UNAWatch/una-hardware/una-watch/electronics/UNAlink_BLUENRG2/UNAlink_BLUENRG2 Rev1.4 Assembly.pdf

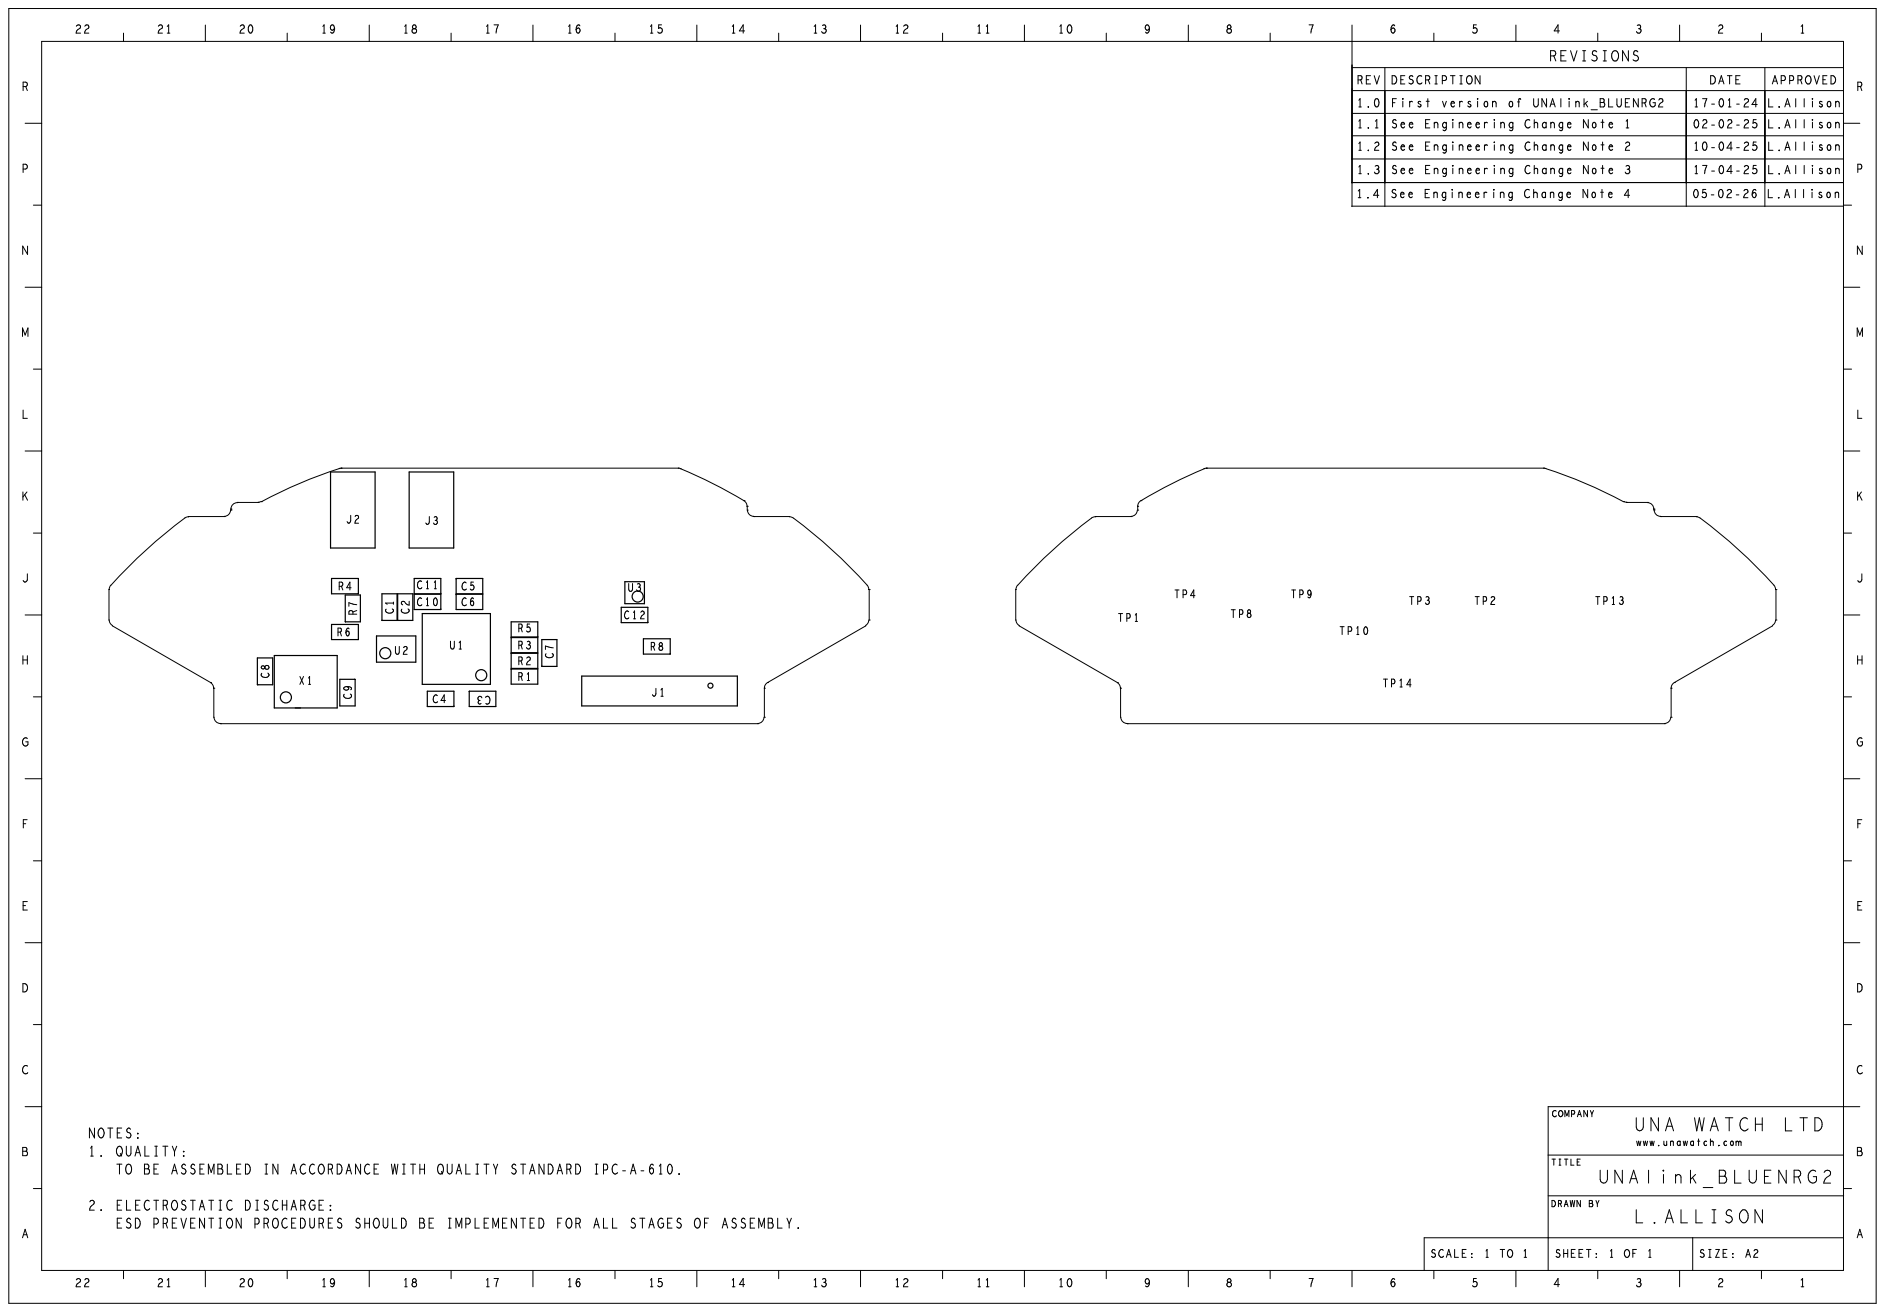
[picture p36: page 1]
