UNAWatch/una-hardware/una-watch/electronics/UNAlink_BLUENRG2/UNAlink_BLUENRG2 Rev1.4 Fabrication.pdf

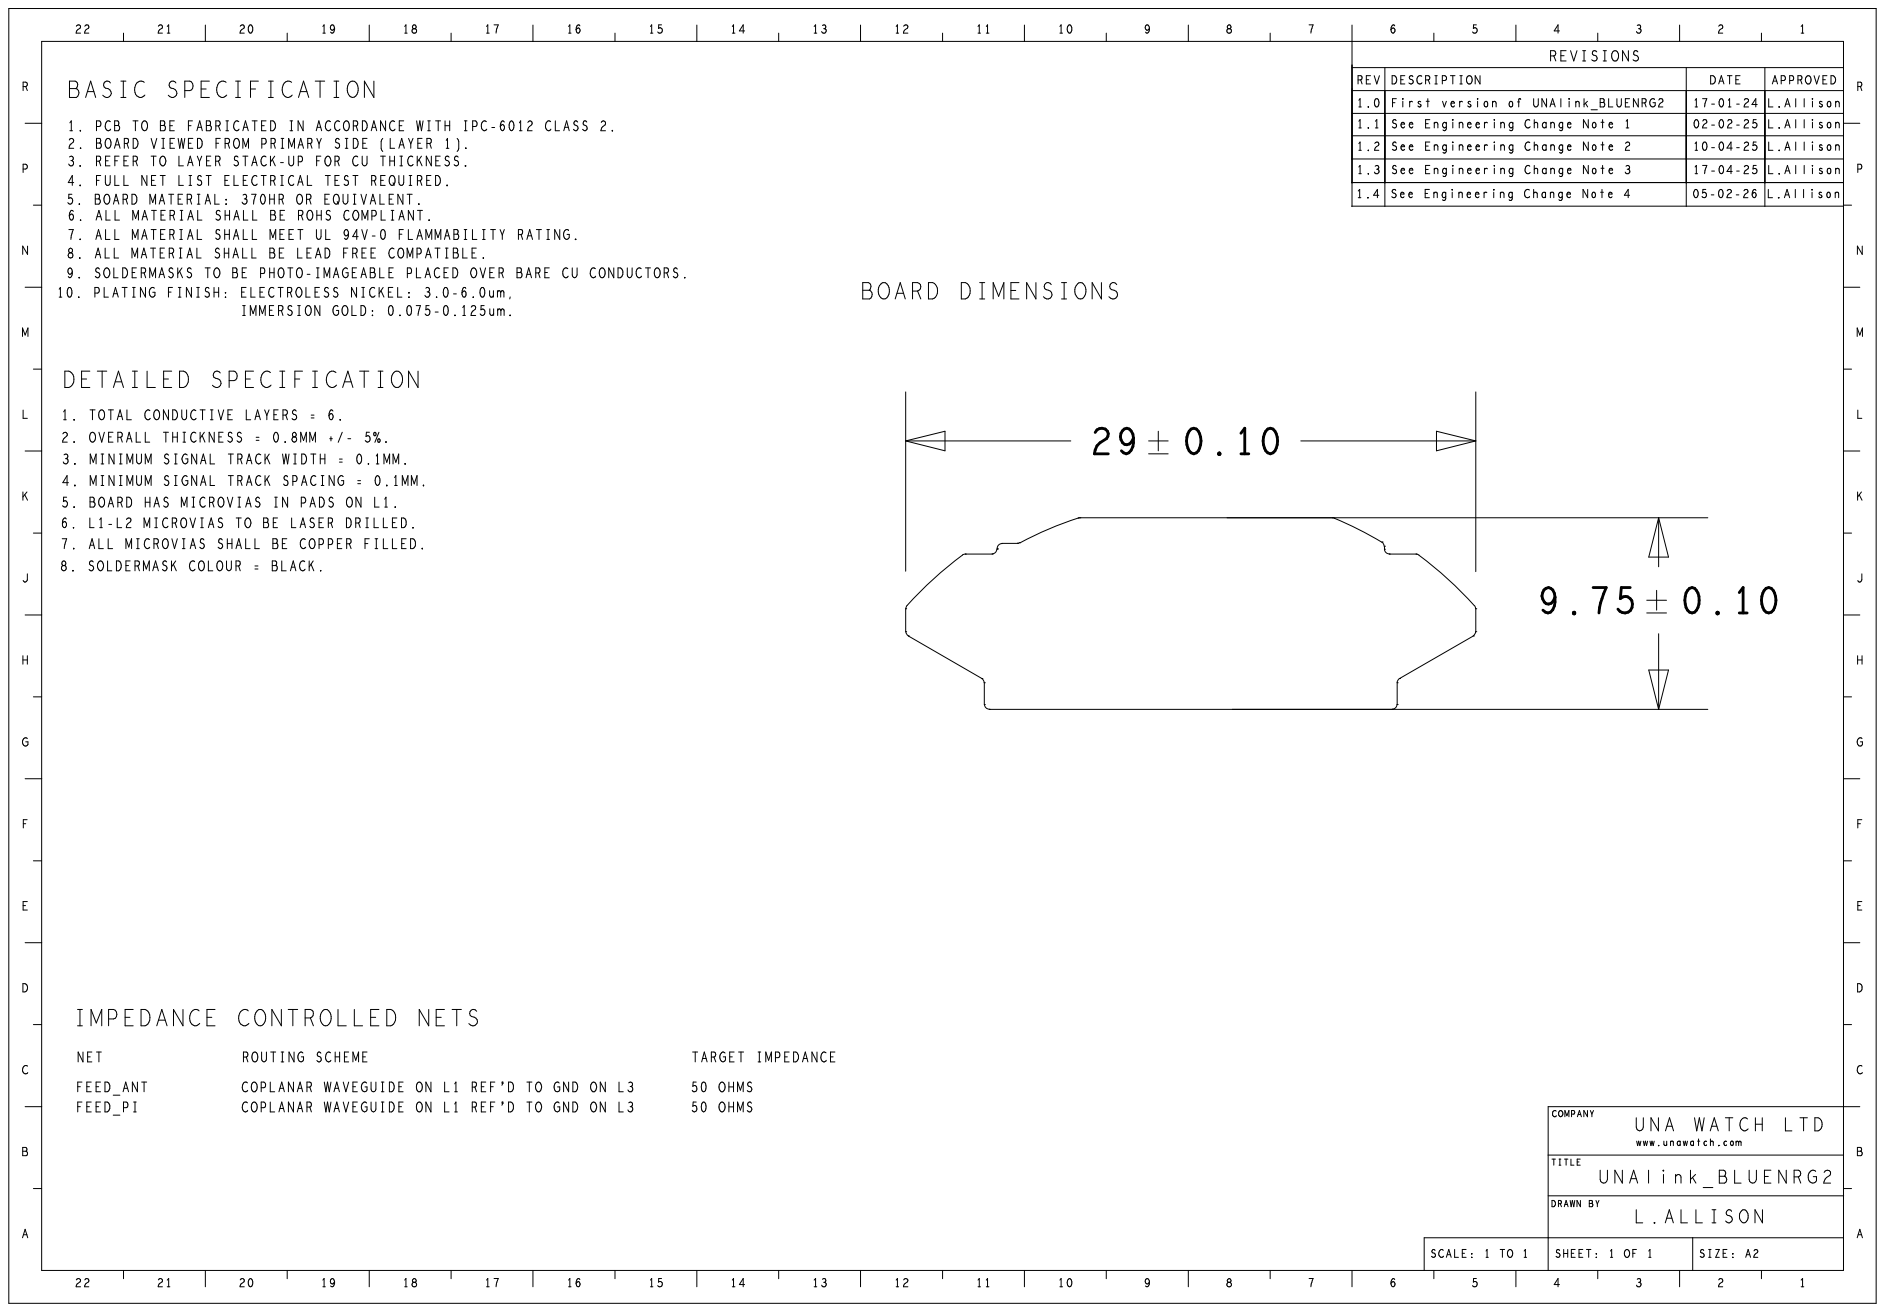
[picture p37: page 1]
