UNAWatch/una-hardware/una-watch/electronics/UNAview_LS012/UNAview_LS012 Rev1.3 Assembly.pdf

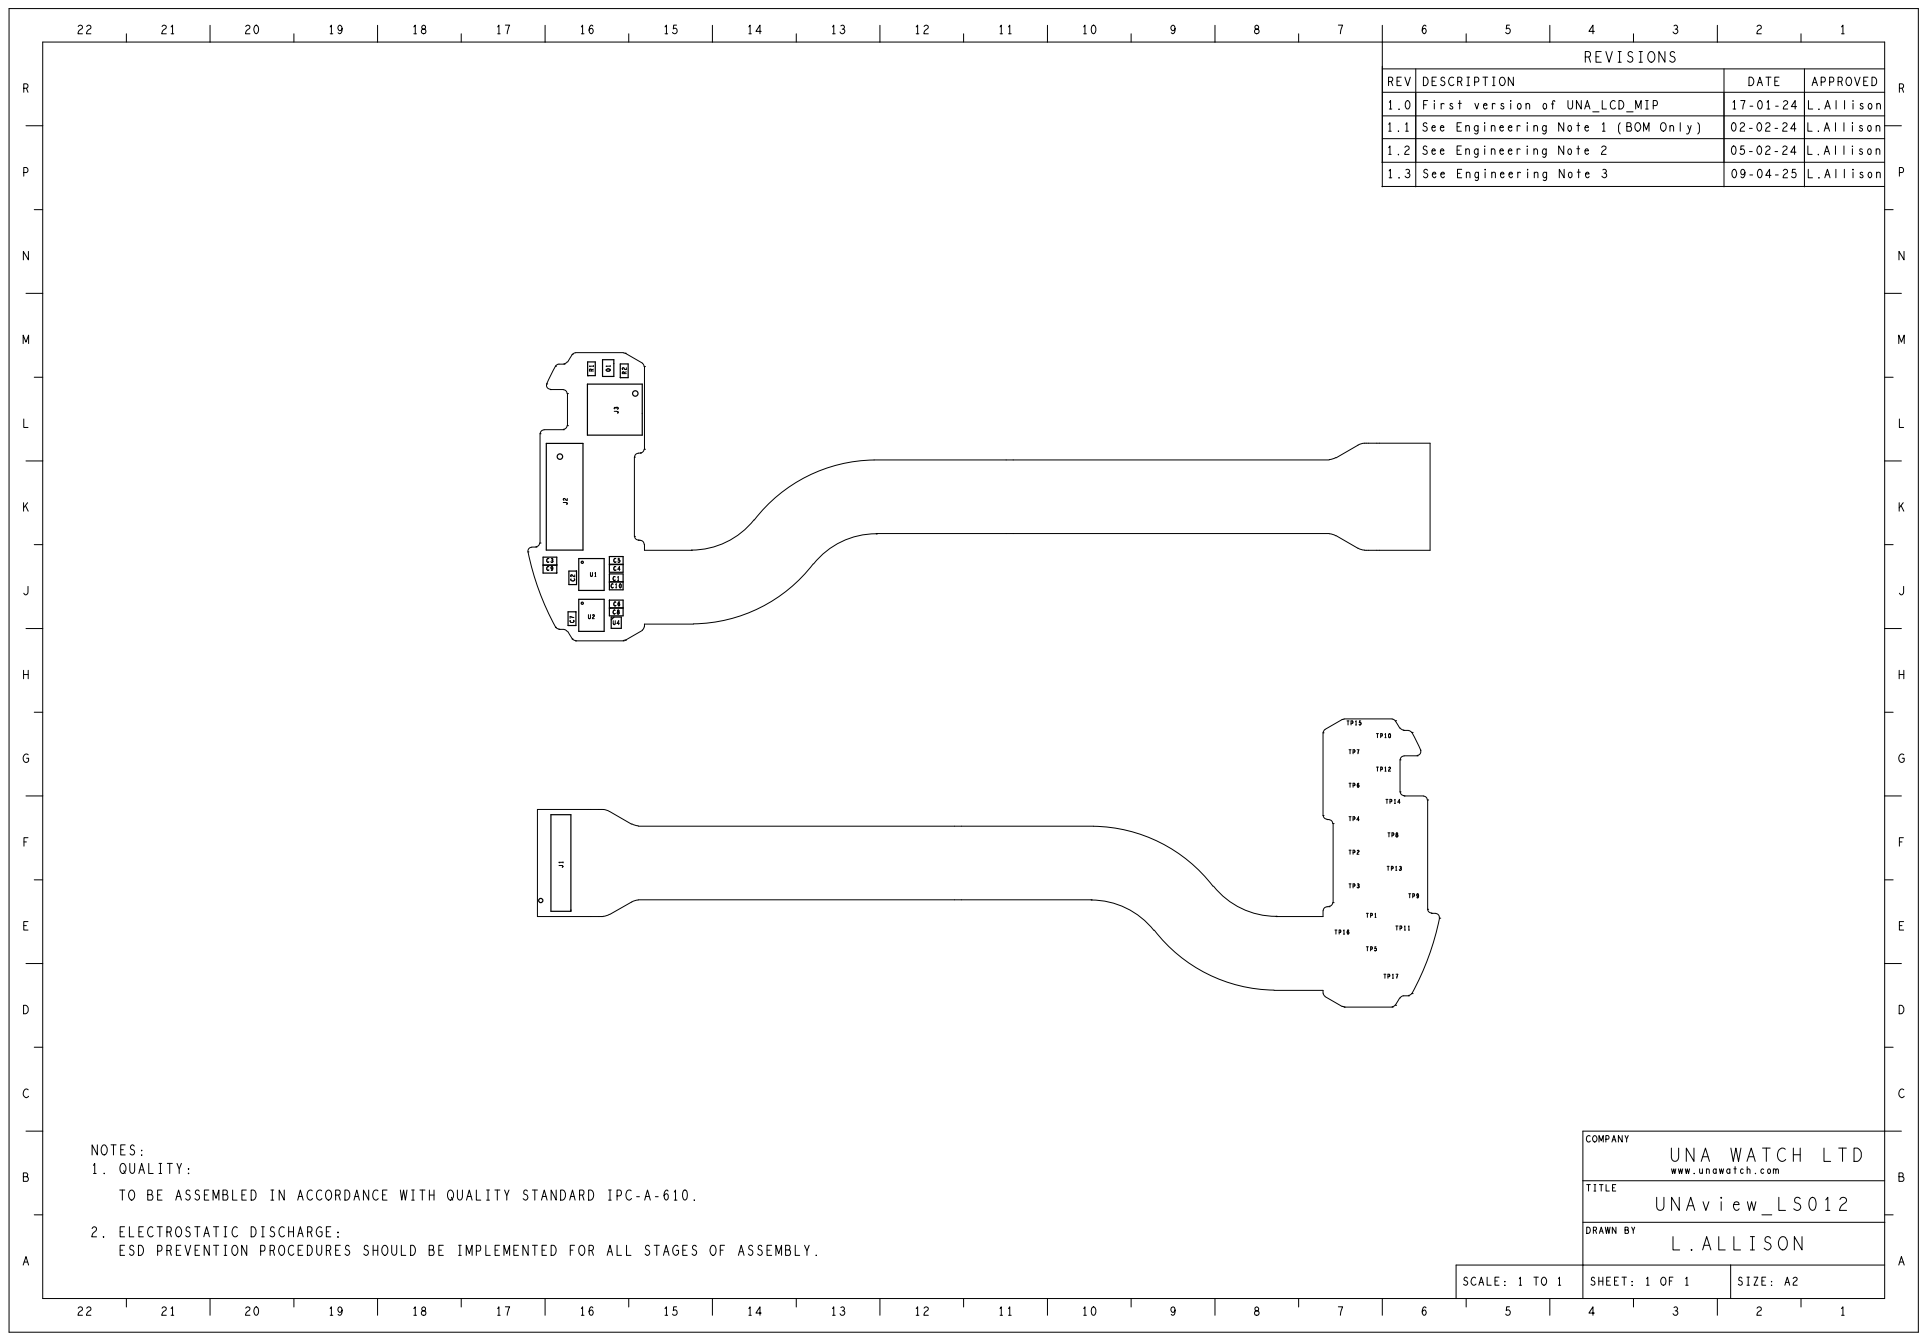
[picture p38: page 1]
