UNAWatch/una-hardware/una-watch/electronics/UNAview_LS012/UNAview_LS012 Rev1.3 Fabrication.pdf

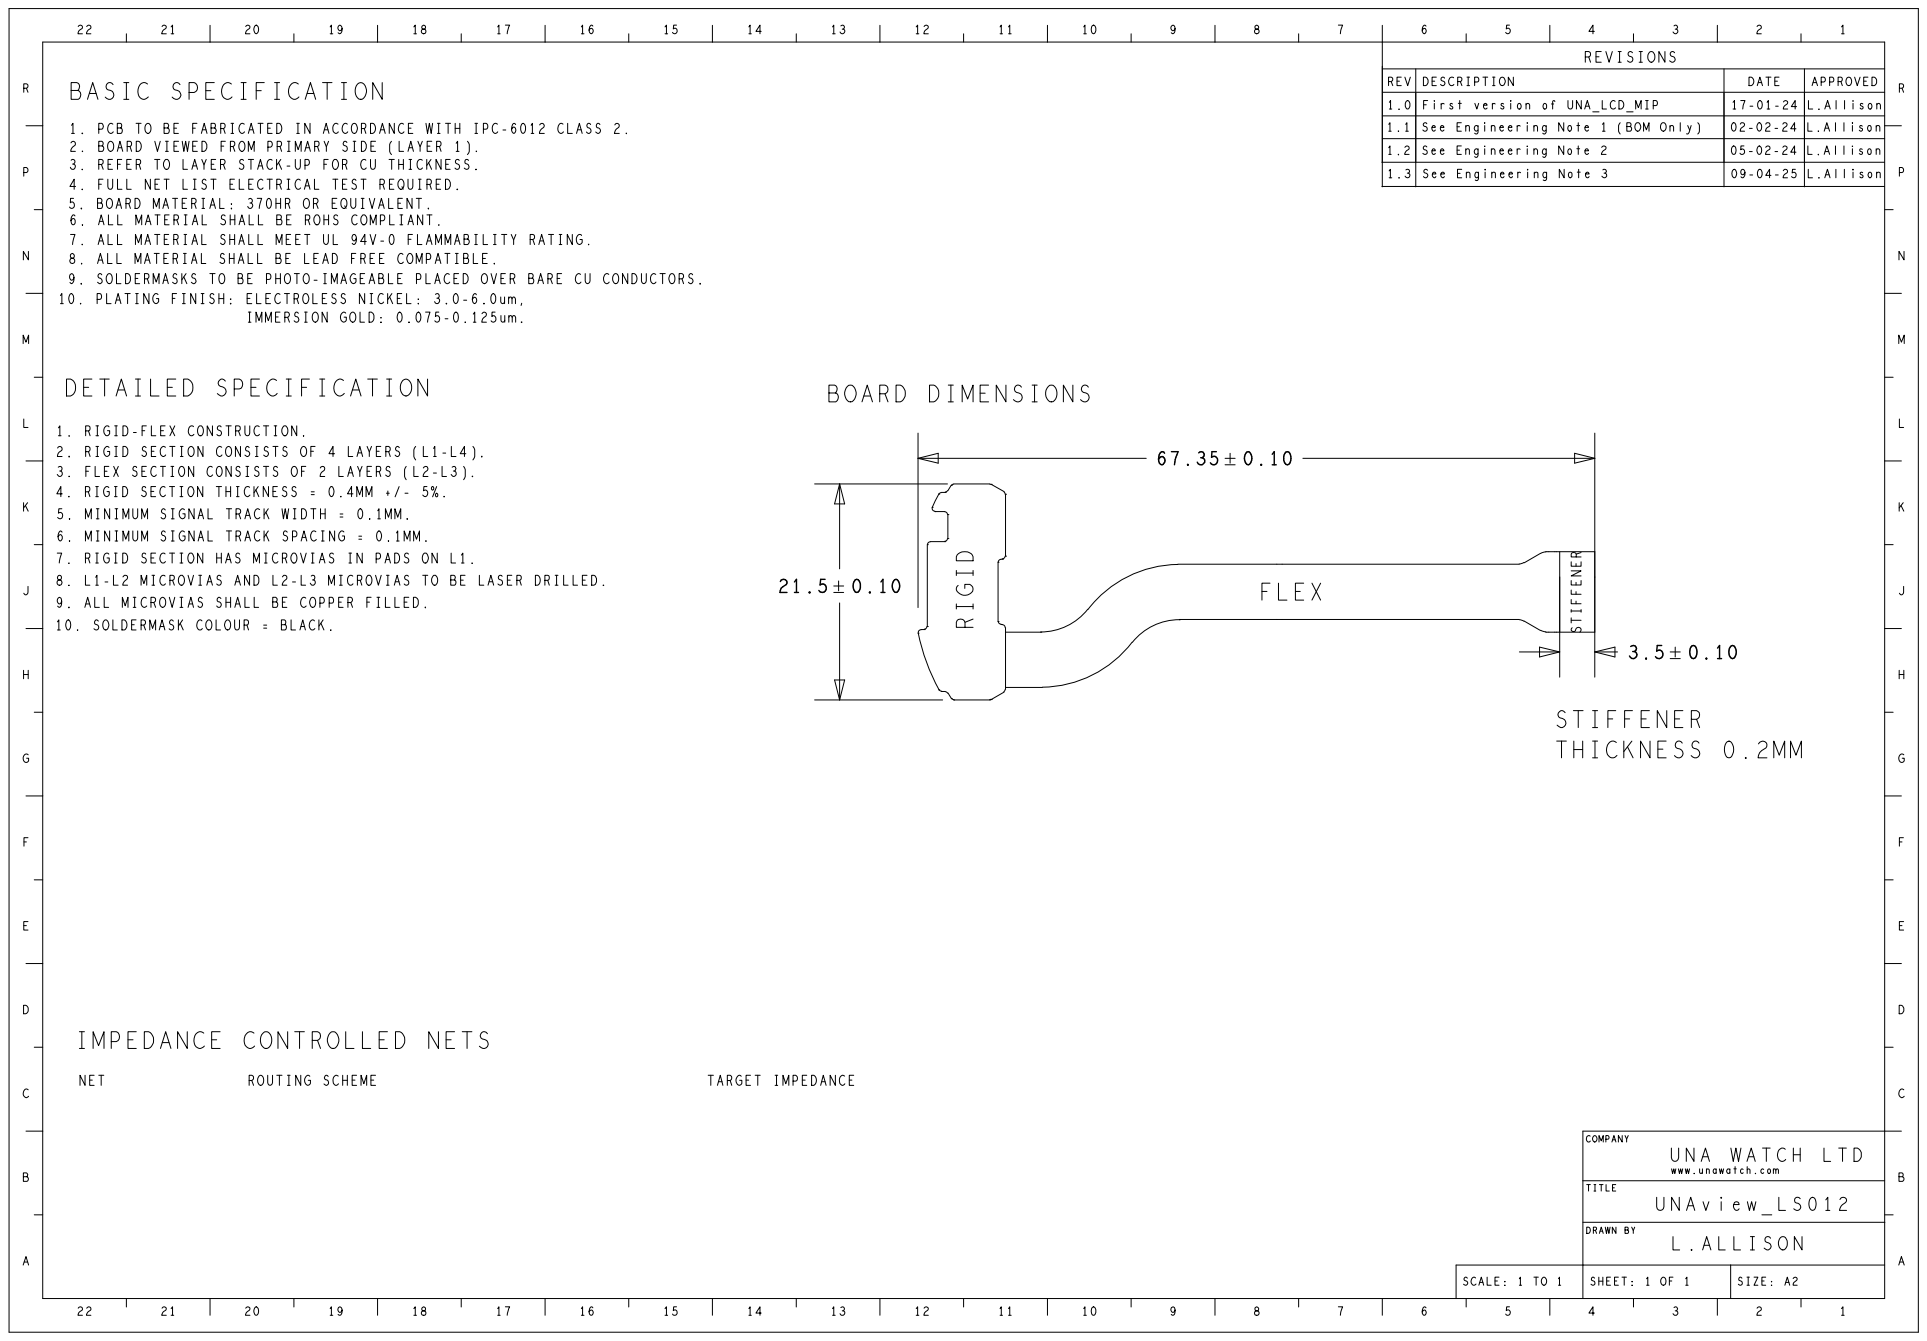
[picture p39: page 1]
