UNAWatch/una-hardware/una-watch/electronics/UNAlink_BLUENRG2/UNAlink_BLUENRG2 Rev1.4 Schematic.pdf

# 01 - Summary

Usage: | UNAlink Module for Una Watch with BLE 5.2

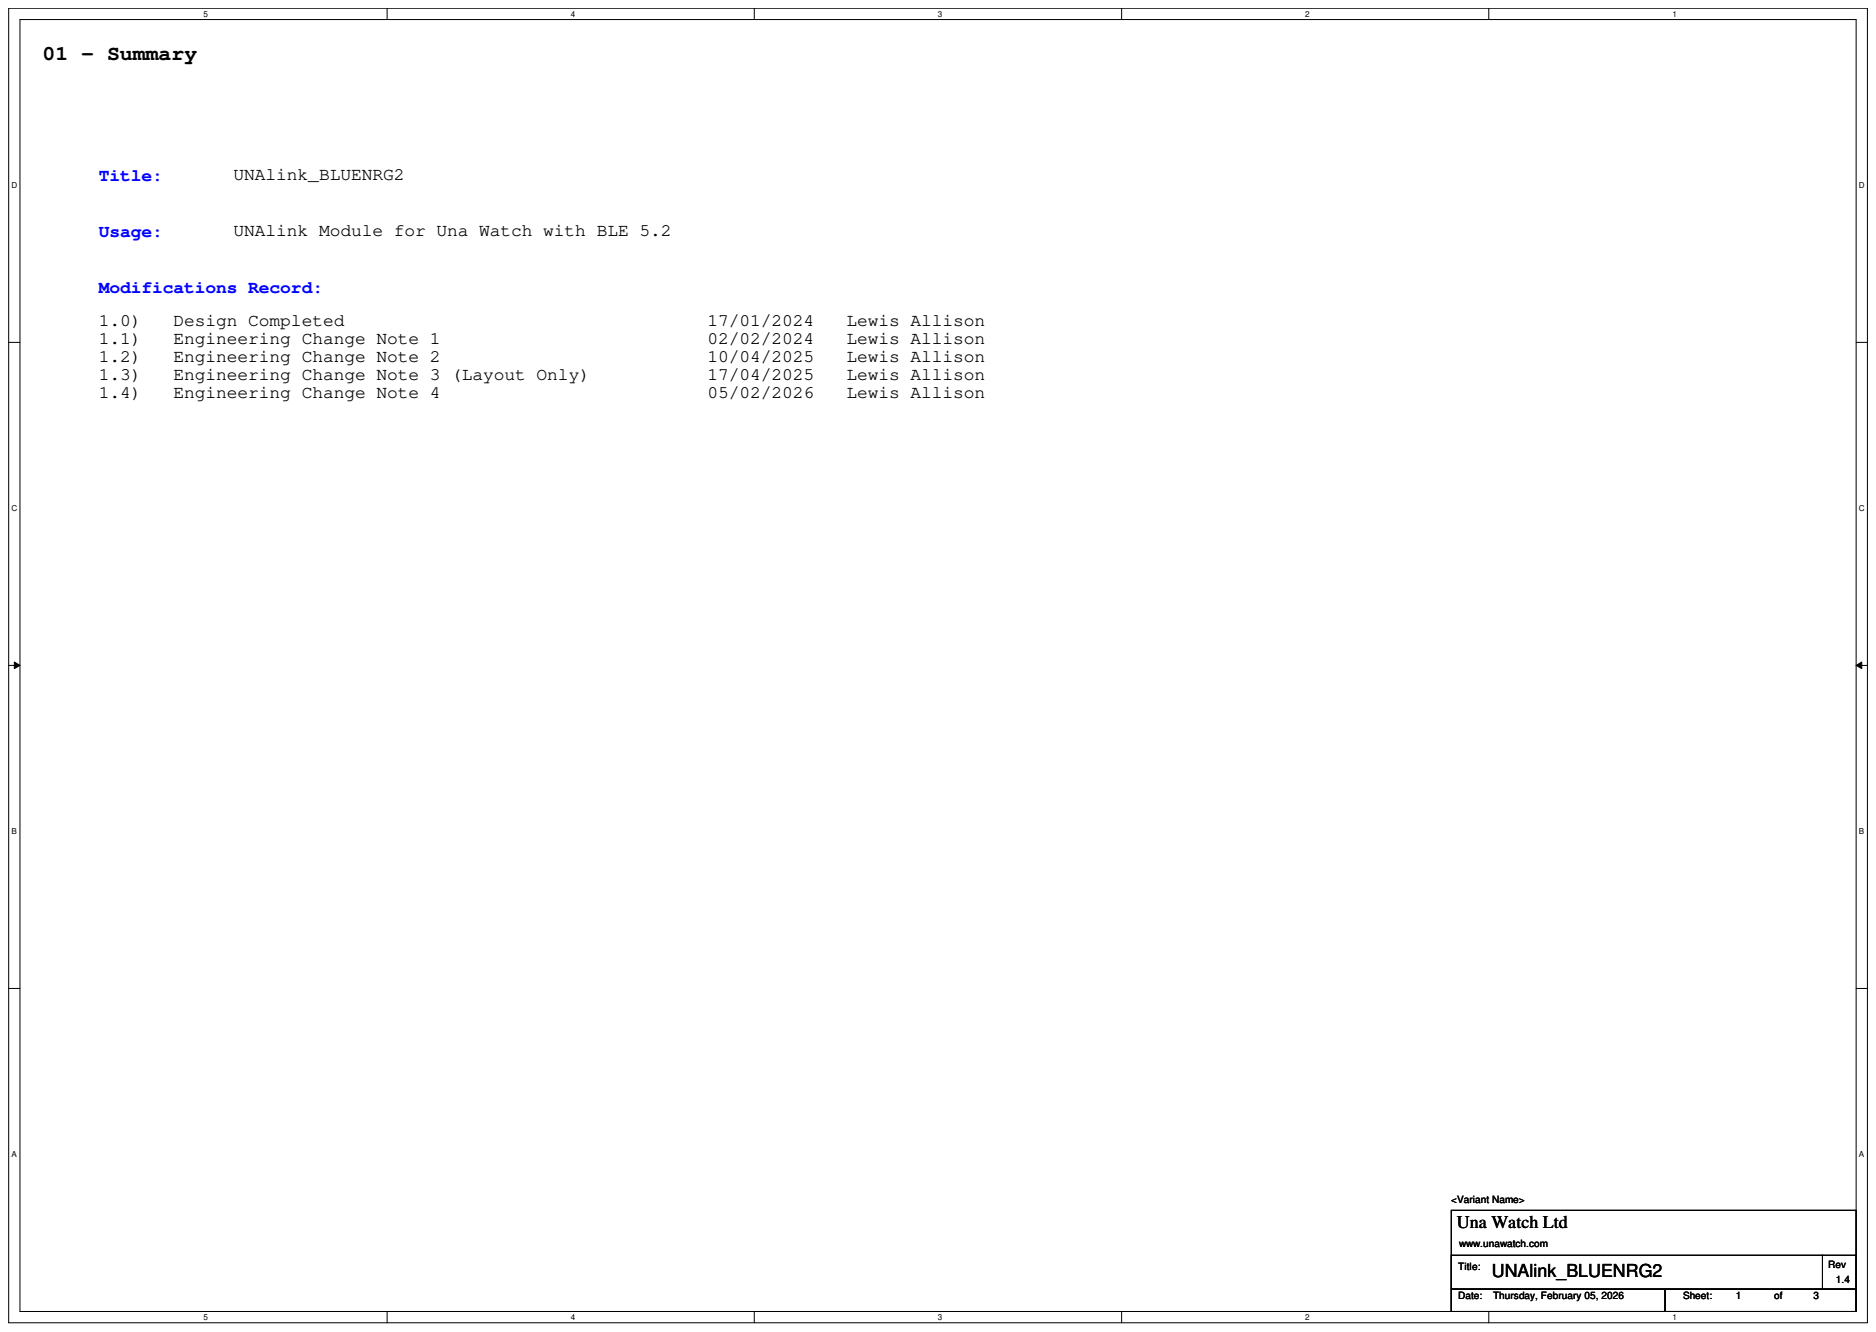
[picture p25: page 1]
Modifications Record:; Title:; UNAlink_BLUENRG2; Design Completed; Lewis Allison; Engineering Change Note 1; Engineering Change Note 2; Engineering Change Note 3 (Layout Only); Engineering Change Note 4; Rev; Date:; Sheet:; 3Thursday, February 05, 2026

<Variant Name>
Una Watch Ltd

www.unawatch.com

# 02 - Main Board Interface

## Main Board Interface

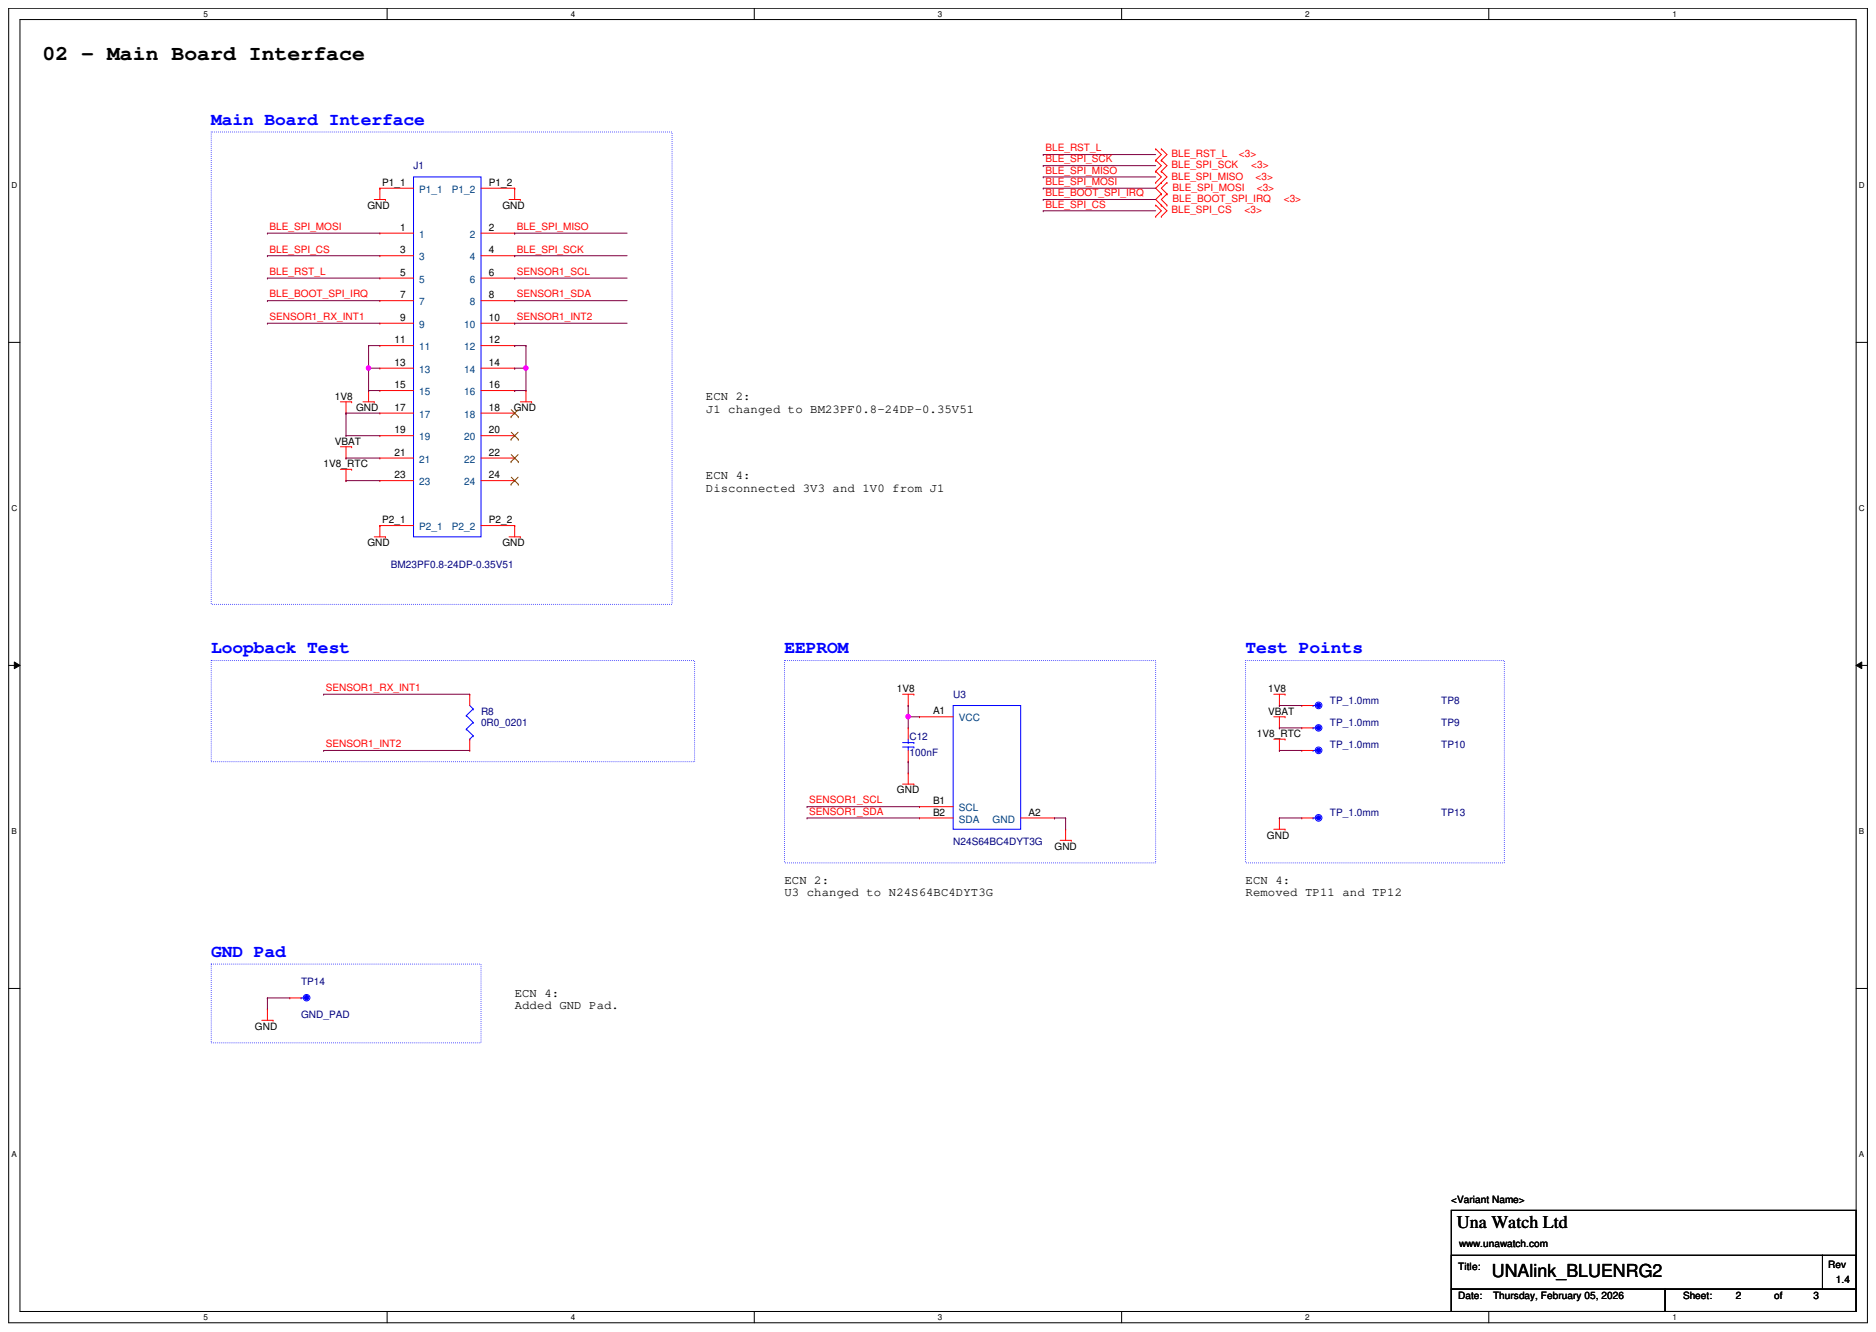
[picture p26: page 2]
Loopback Test; EEPROM; Test Points; ECN 2: J1 changed to BM23PF0.8-24DP-0.35V51; ECN 2: U3 changed to N24S64BC4DYT3G; GND Pad; ECN 4: Removed TP11 and TP12; GND; VBAT; 1V8_RTC; BLE_RST_L <3>; BLE_SPI_SCK; BLE_SPI_MISO; BLE_SPI_MOSI; BLE_BOOT_SPI_IRQ; BLE_SPI_CS; GND_PAD; N24S64BC4DYT3G; VCC A1; SCL B1; SDA B2; BLE_RST_L BLE_SPI_SCK BLE_SPI_MISO BLE_SPI_MOSI BLE_BOOT_SPI_IRQ BLE_SPI_CS; SENSOR1_SCL; SENSOR1_SDA; SENSOR1_RX_INT1; BLE_RST_L; SENSOR1_INT2; SENSOR1_SCL SENSOR1_SDA

ECN 4:
Disconnected 3V3 and 1V0 from J1

Added GND Pad.

<Variant Name>
Una Watch Ltd

www.unawatch.com

# 03 - BLE

## BLE 5.2 Network Processor

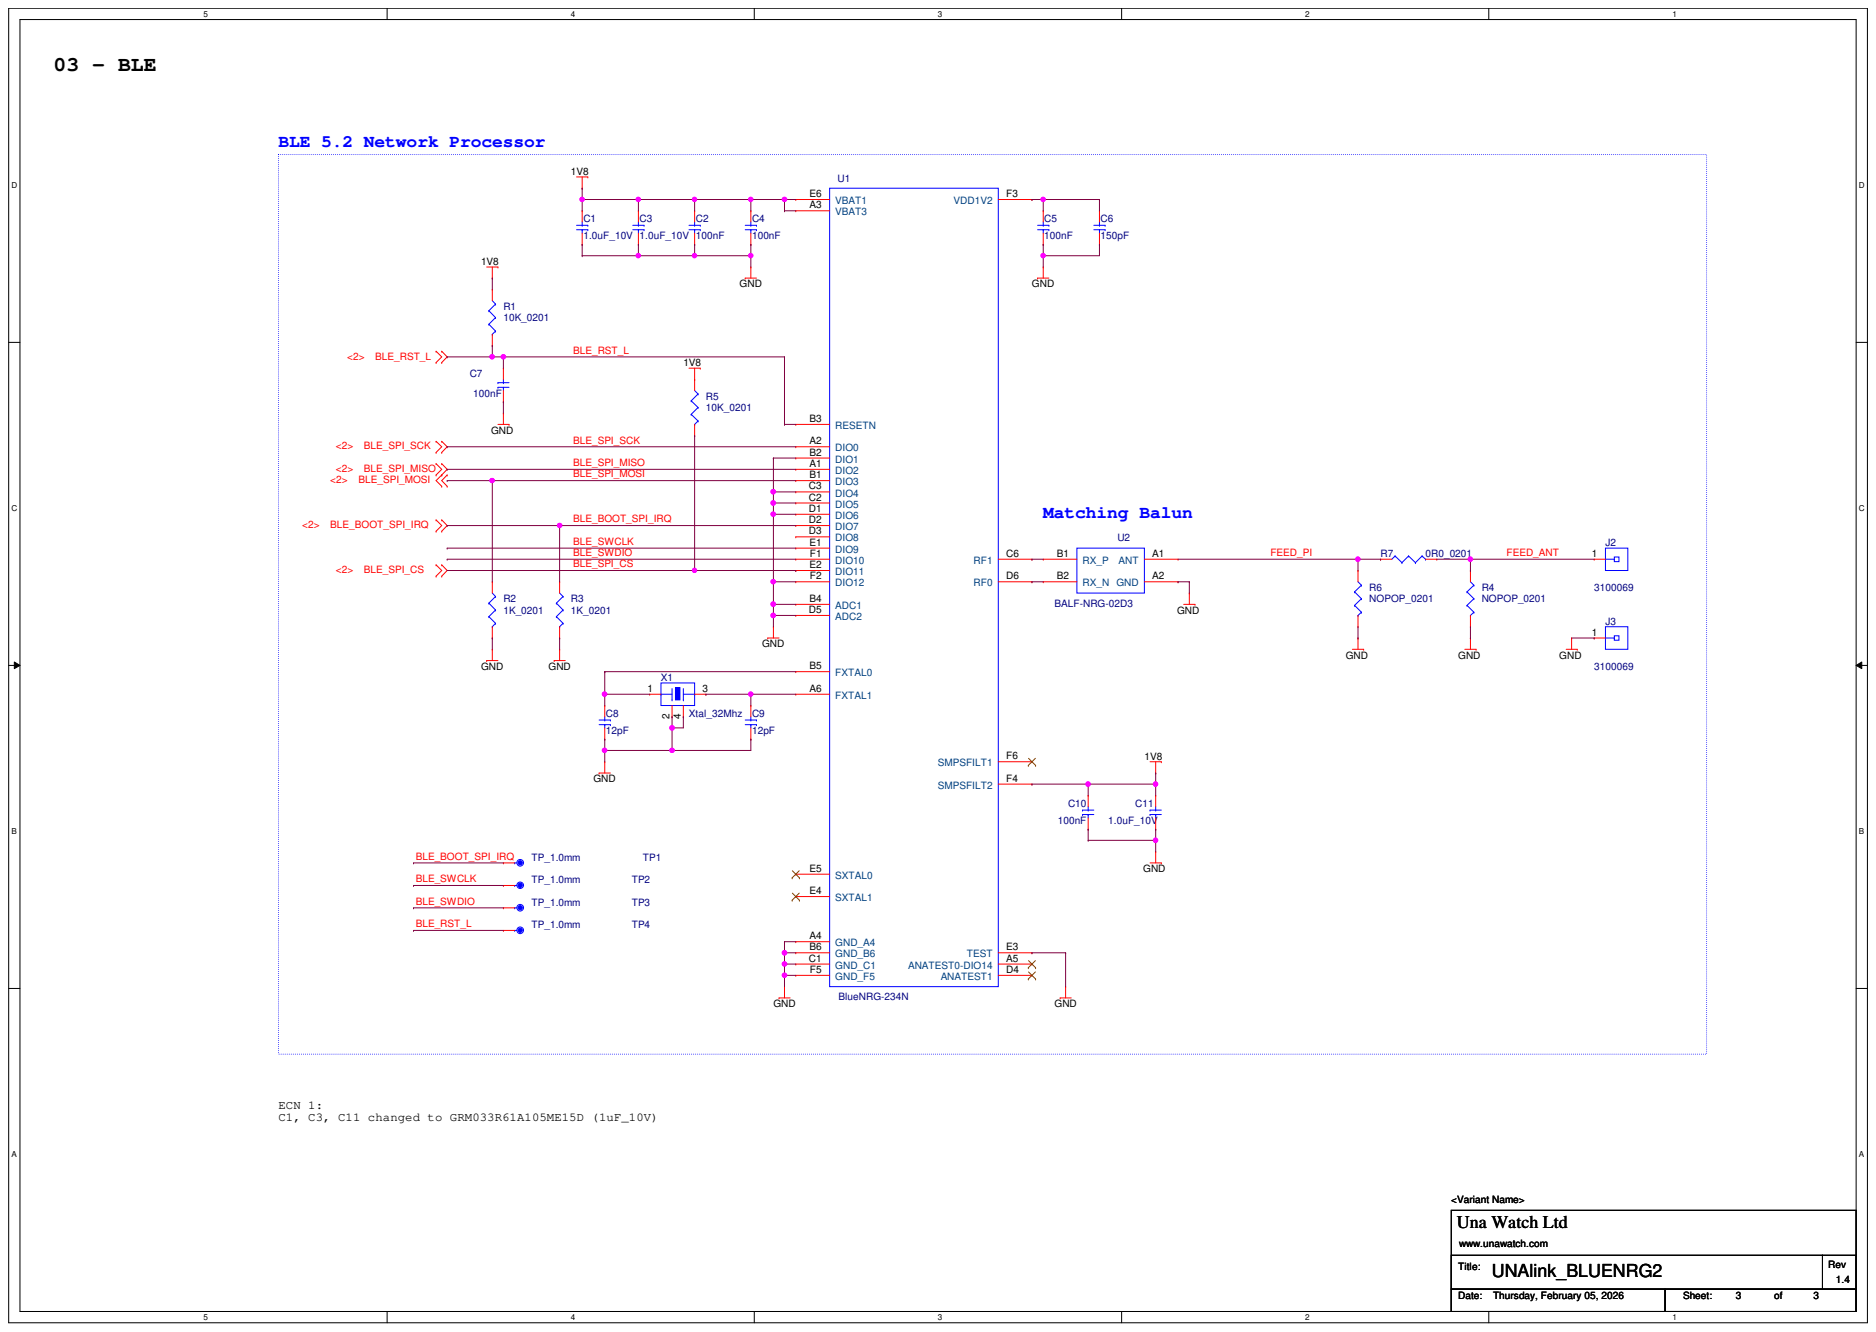
[picture p27: page 3]
