UNAWatch/una-hardware/una-watch/electronics/UNAview_LS012/UNAview_LS012 Rev1.3 Schematic.pdf

# 01 - Summary

Usage: | LCD PCB for Una Watch for MIP LCD

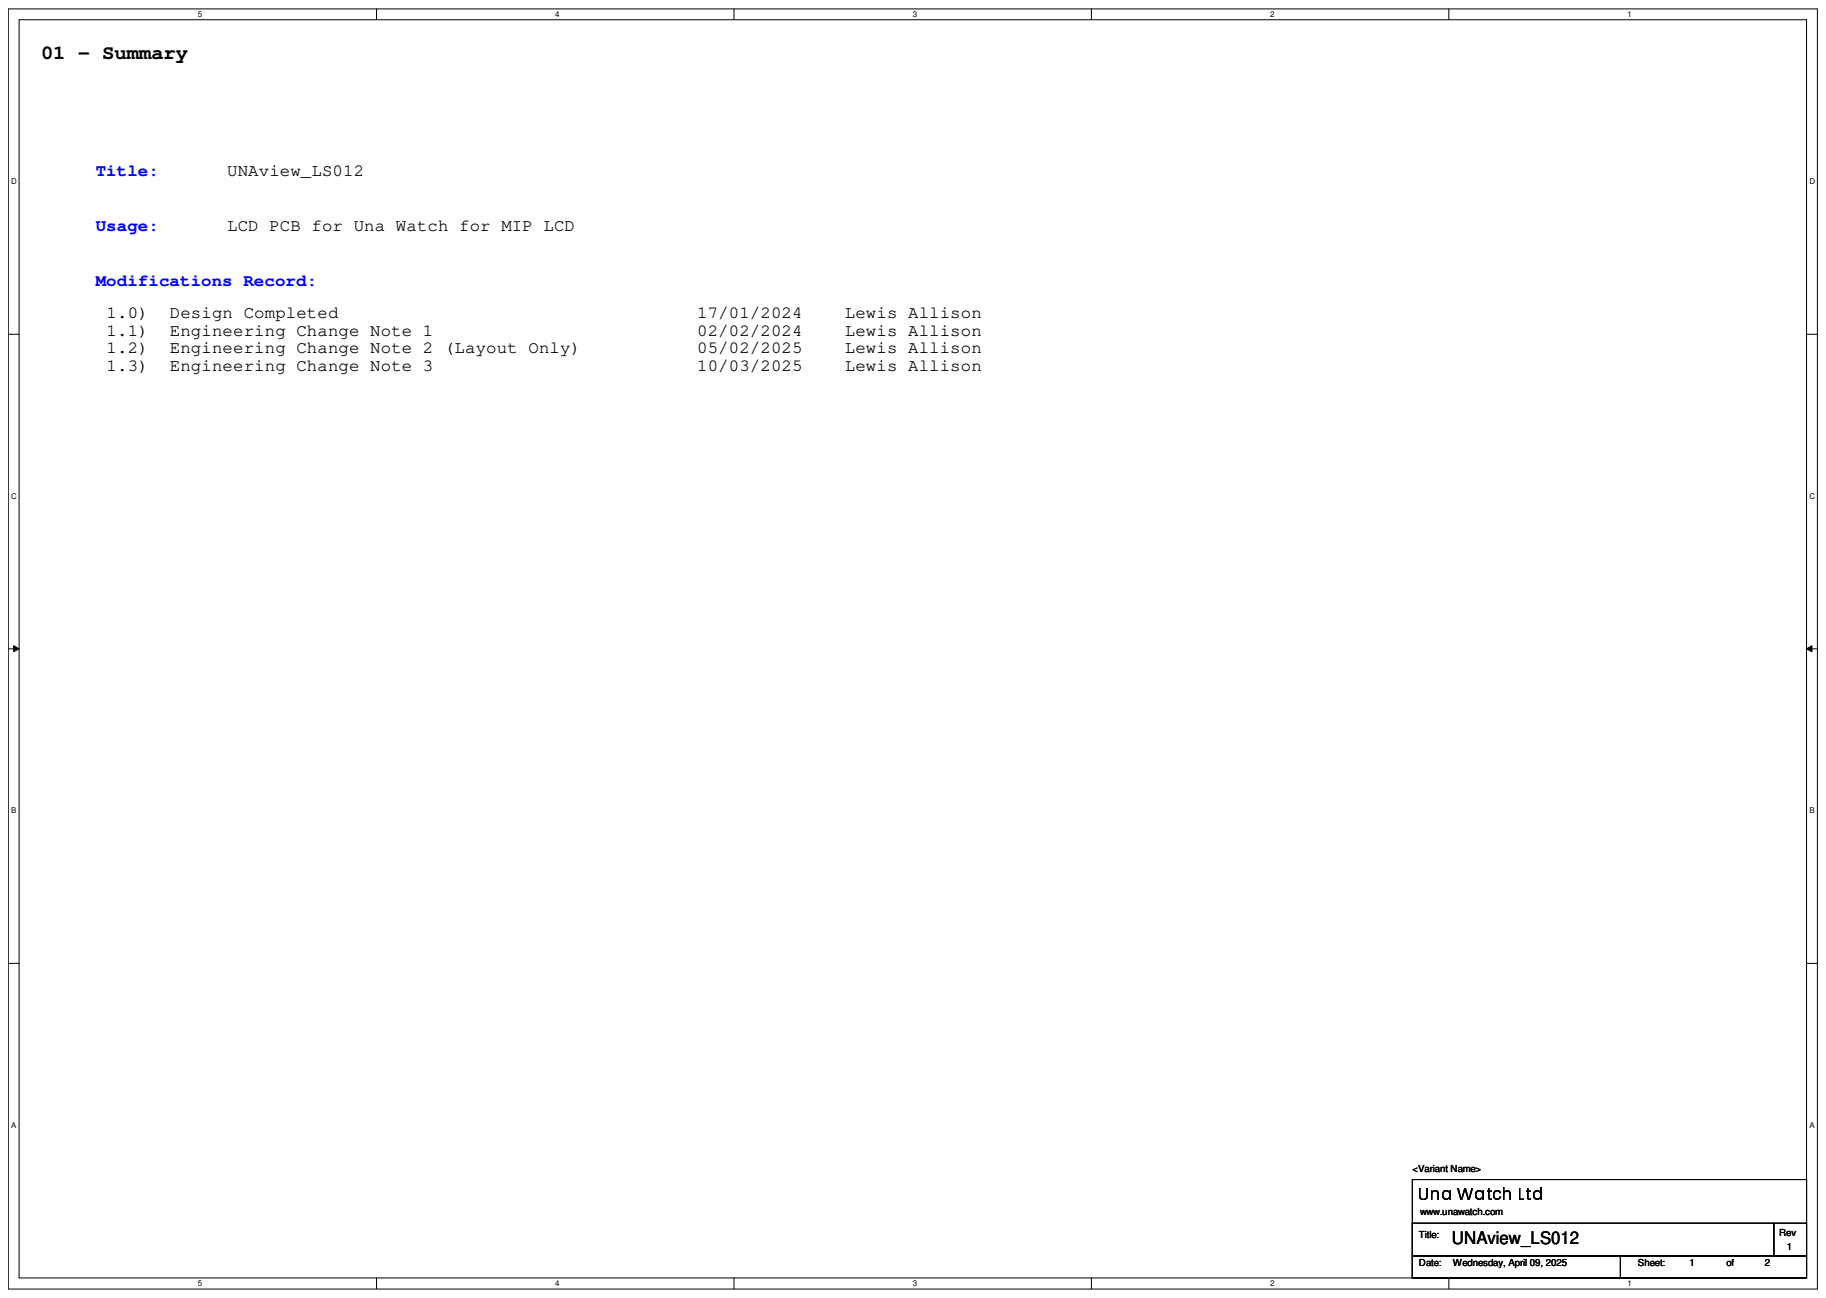
[picture p28: page 1]
Modifications Record:; Title:; UNAview_LS012; Design Completed; Lewis Allison; Engineering Change Note 1; Engineering Change Note 2 (Layout Only); Engineering Change Note 3; Rev; Date:; Sheet:; 2Wednesday, April 09, 2025; <Variant Name>

www.unawatch.com

# 02 - MIP Interface

tors, 1.8V <-> 3.3V | 21-pin FPC for LCDMain Board Interface | Level Transla

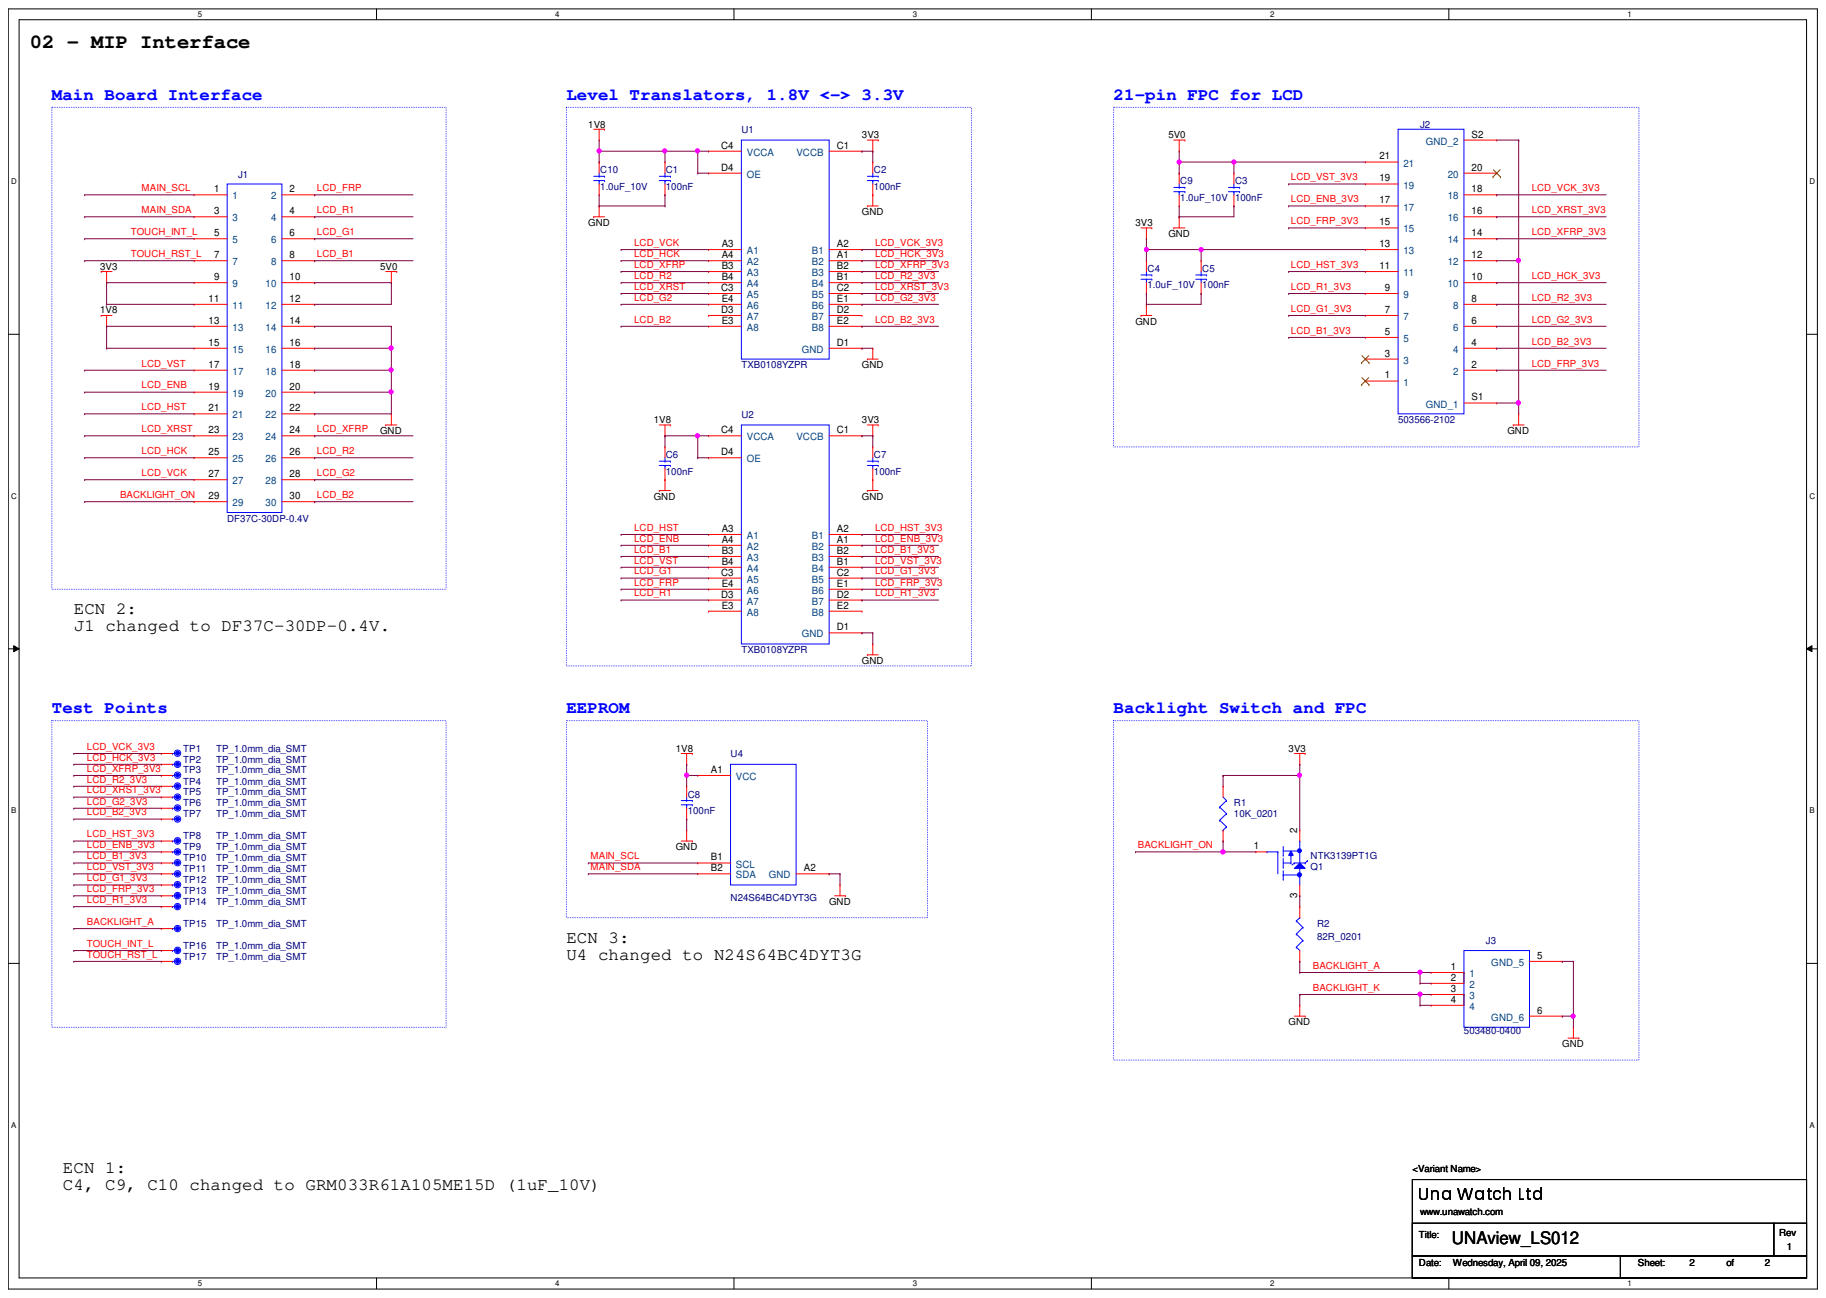
[picture p29: page 2]

Backlight Switch and FPCEEPROMTest Points
